robbe-dc/Basalt/parts/3d/motherboard bottom back/README.md

# Motherboard bottom back

This part connects the motherboard bottom back to the 2 back extrusions and has room for 4 magnets for the back and 2 side panels.

This part can be printed without support provided that your printer can print overhangs of about 50 degree.

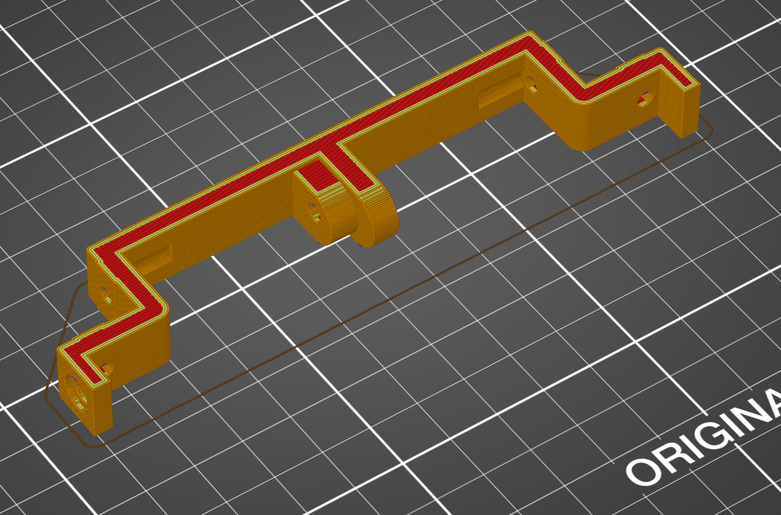
[picture p15: parts/3d/motherboard bottom back/screenshot.png]
Slicer screenshot
