robbe-dc/Basalt/parts/3d/psu bottom/README.md

# PSU bottom

This part has several uses. It connacts the bottom of the PSU to the 2 back extrusions while also clamping the PCI bracket of the GPU into place. Print upside down for and easy supportless print.

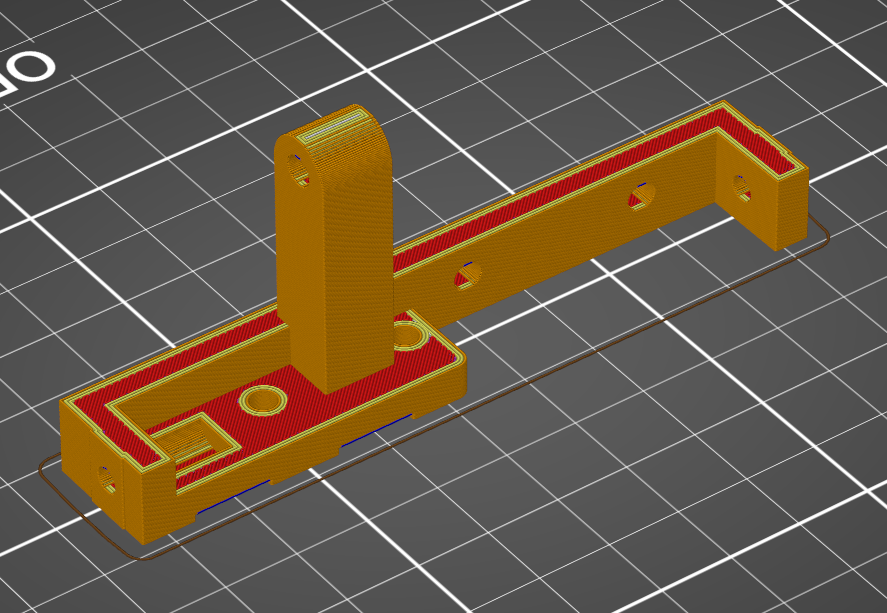
[picture p17: parts/3d/psu bottom/screenshot.png]
Slicer screenshot
