robbe-dc/Basalt/parts/3d/psu top/README.md

# PSU top

This part connects the top of the PSU to one of the back extrusions. Easy and straightforward print.

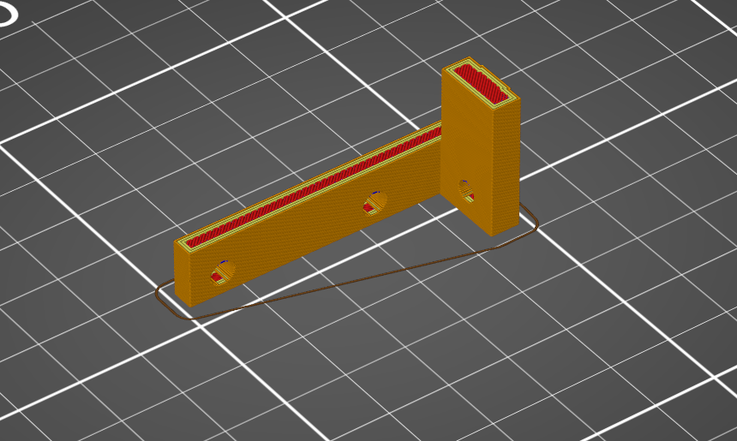
[picture p18: parts/3d/psu top/screenshot.png]
Slicer screenshot
