robbe-dc/Basalt/parts/3d/motherboard bottom front/motherboard bottom front magnet.stl

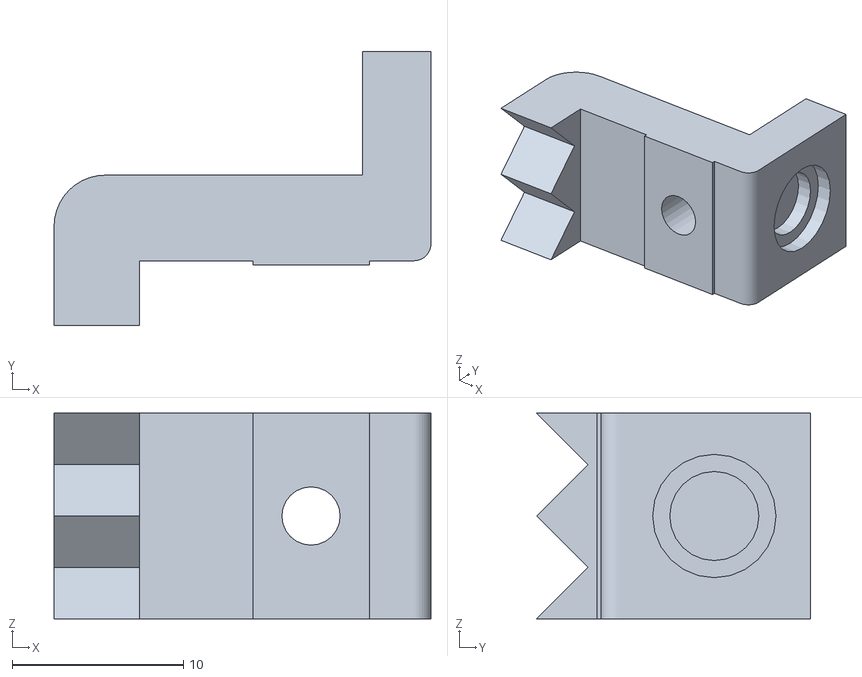
[picture p33: CAD file, 2021-04-11]
parts/3d/motherboard bottom front/motherboard bottom front magnet.stl
22.0 x 16.0 x 12.0
